lucianoaguerre/Burn-in-test/Firmware/Server/config.h

byte   dev_state[100];
const char* ssid     = "FV-IOT";
const char* password = "FVVR#iot1980";
const char* hostname = "ESP32";

IPAddress ip(192, 168, 1, 200);
IPAddress gateway(192, 168, 1, 1);
IPAddress subnet(255, 255, 255, 0);
