lucianoaguerre/Burn-in-test/Firmware/Server/API.hpp

//byte   dev_state[100];

void setData(AsyncWebSocketClient * client, String request)
{
  StaticJsonDocument<200> doc;
  DeserializationError error = deserializeJson(doc, request);
  if (error) { return; }

  int id = doc["id"];
  bool ledStatus = doc["status"];
  Serial.println(id);
  Serial.println(ledStatus);
}

void getData(AsyncWebSocketClient * client, String request)
{
   String response;
   StaticJsonDocument<1600> jsonDoc;
   jsonDoc["id00"] = dev_state[0];
   jsonDoc["id01"] = dev_state[1];
   jsonDoc["id02"] = dev_state[2];
   jsonDoc["id03"] = dev_state[3];
   jsonDoc["id04"] = dev_state[4];
   jsonDoc["id05"] = dev_state[5];
   jsonDoc["id06"] = dev_state[6];
   jsonDoc["id07"] = dev_state[7];
   jsonDoc["id08"] = dev_state[8];
   jsonDoc["id09"] = dev_state[9];
   
   jsonDoc["id10"] = dev_state[10];
   jsonDoc["id11"] = dev_state[11];
   jsonDoc["id12"] = dev_state[12];
   jsonDoc["id13"] = dev_state[13];
   jsonDoc["id14"] = dev_state[14];
   jsonDoc["id15"] = dev_state[15];
   jsonDoc["id16"] = dev_state[16];
   jsonDoc["id17"] = dev_state[17];
   jsonDoc["id18"] = dev_state[18];
   jsonDoc["id19"] = dev_state[19];
   
   jsonDoc["id20"] = dev_state[20];
   jsonDoc["id21"] = dev_state[21];
   jsonDoc["id22"] = dev_state[22];
   jsonDoc["id23"] = dev_state[23];
   jsonDoc["id24"] = dev_state[24];
   jsonDoc["id25"] = dev_state[25];
   jsonDoc["id26"] = dev_state[26];
   jsonDoc["id27"] = dev_state[27];
   jsonDoc["id28"] = dev_state[28];
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
   jsonDoc["id95"] = dev_state[95];
   jsonDoc["id96"] = dev_state[96];
   jsonDoc["id97"] = dev_state[97];
   jsonDoc["id98"] = dev_state[98];
   jsonDoc["id99"] = dev_state[99];
      
   serializeJson(jsonDoc, response);
   client->text(response);
   serializeJsonPretty(jsonDoc, Serial);
}
