lucianoaguerre/Burn-in-test/Firmware/test-module/Hardware_Def.h

/******************************************************************************
* Hardware definitions
*******************************************************************************/

#define LED_RED     27 
#define LED_GREEN   13
#define VIN         32
#define ACT         26 

//**** END OF FILE **********************************************************************
