lucianoaguerre/Burn-in-test/Firmware/test-module/BLE_Functions.hpp

/******************************************************************************
* Module includes
*******************************************************************************/
#include <BLEDevice.h>
#include <BLEServer.h>
#include <BLEUtils.h>
#include <BLE2902.h>

/******************************************************************************
* Variable Definitions
*******************************************************************************/
BLEServer *pServer = NULL;
BLECharacteristic * pTxCharacteristic;
bool deviceConnected = false;
bool oldDeviceConnected = false;
uint8_t txValue = 0;


#define SERVICE_UUID           "6E400001-B5A3-F393-E0A9-E50E24DCCA9E" 
#define CHARACTERISTIC_UUID_RX "6E400002-B5A3-F393-E0A9-E50E24DCCA9E"
#define CHARACTERISTIC_UUID_TX "6E400003-B5A3-F393-E0A9-E50E24DCCA9E"
#define DEVICE_NAME            "PIXART-BI-001"

//******************************************************************************
class MyServerCallbacks: public BLEServerCallbacks 
{
    void onConnect(BLEServer* pServer) 
    {
      deviceConnected = true;
    };

    void onDisconnect(BLEServer* pServer) 
    {
      deviceConnected = false;
    }
};

class MyCallbacks: public BLECharacteristicCallbacks 
{
    void onWrite(BLECharacteristic *pCharacteristic) 
    {
      std::string rxValue = pCharacteristic->getValue();
      if (rxValue.length() > 0) 
      {
        Serial.print("Received Value: ");
        for (int i = 0; i < rxValue.length(); i++)
        {
          Serial.print(rxValue[i]);
        }
        Serial.println();
        Serial.print("notify value: ");
        pTxCharacteristic->setValue(&test_state, 1);
        Serial.println(test_state);
        pTxCharacteristic->notify();
      }
    }
};


void BLE_setup(void) 
{

  BLEDevice::init(DEVICE_NAME);
  pServer = BLEDevice::createServer();
  pServer->setCallbacks(new MyServerCallbacks());
  BLEService *pService = pServer->createService(SERVICE_UUID);

  pTxCharacteristic = pService->createCharacteristic
              (
                    CHARACTERISTIC_UUID_TX,
                    BLECharacteristic::PROPERTY_NOTIFY
              );
                      
  pTxCharacteristic->addDescriptor(new BLE2902());

  BLECharacteristic * pRxCharacteristic = pService->createCharacteristic
              (
                    CHARACTERISTIC_UUID_RX,
                    BLECharacteristic::PROPERTY_WRITE
              );

  pRxCharacteristic->setCallbacks(new MyCallbacks());
  pService->start();
  pServer->getAdvertising()->start();
  Serial.println("Waiting a client connection to notify...");
}
